leethomason/OpenSaber/parts/shapes.scad

FACES   = 180;
EPSILON = 0.1;
PIN	    = 2.54;


module tube(h=1, inner=0, outer=0, di=0, do=0) {
    rInner = inner > 0 ? inner : di / 2;
    rOuter = outer > 0 ? outer : do / 2;

	if (rInner >= rOuter) echo("ERROR in tube. rOuter must be > rInner.");

	difference() {
		cylinder(h=h, r=rOuter);
		translate([0,0,-EPSILON]) {
			cylinder(h=h + EPSILON*2, r=rInner);
		}
	}
}

module roundedRect(size, r, up="z")
{
	if (up == "x") {
		H = size[0];
		hull()
		{
			translate([0, r, r]) rotate([0, 90, 0]) cylinder(r=r, h=H);
			translate([0, size[1] - r, r]) rotate([0, 90, 0]) cylinder(r=r, h=H);
			translate([0, r, size[2] - r]) rotate([0, 90, 0]) cylinder(r=r, h=H);
			translate([0, size[1] - r, size[2] - r]) rotate([0, 90, 0]) cylinder(r=r, h=H);
		}
	}
	else if (up == "y") {
		H = size[1];
		hull()
		{
			translate([r, 0, r]) rotate([-90, 0, 0]) cylinder(r=r, h=H);
			translate([size[0] - r, 0, r]) rotate([-90, 0, 0]) cylinder(r=r, h=H);
			translate([r, 0, size[2] - r]) rotate([-90, 0, 0]) cylinder(r=r, h=H);
			translate([size[0] - r, 0, size[2] - r]) rotate([-90, 0, 0]) cylinder(r=r, h=H);
		}
	}
	else {
		H = size[2];
		hull()
		{
			translate([r, r, 0])  cylinder(r=r, h=H);
			translate([size[0] - r, r, 0])  cylinder(r=r, h=H);
			translate([r, size[1] - r, 0])  cylinder(r=r, h=H);
			translate([size[0] - r, size[1] - r, 0])  cylinder(r=r, h=H);
		}
	}
}

module cubePair(x, size)
{
	translate([x, 0, 0])
		cube(size=size);
	mirror([1,0,0]) translate([x, 0, 0])
		cube(size=size);
}

module polygonXY(h, points)
{
    linear_extrude(height = h) {
        polygon(points=points);
    }  
}

module polygonYZ(h, points)
{
    multmatrix(m = [ [0, 0, 1, 0],
    				 [1, 0, 0, 0],
    				 [0, 1, 0, 0],
    				 [0, 0, 0, 1]
       			   ])
    linear_extrude(height = h) {
        polygon(points=points);
    }  	
}

module polygonZY(h, points)
{
    multmatrix(m = [ [0, 0, 1, 0],
    				 [0, 1, 0, 0],
    				 [1, 0, 0, 0],
    				 [0, 0, 0, 1]
       			   ])
    linear_extrude(height = h) {
        polygon(points=points);
    }  	
}
module polygonXZ(h, points)
{
    multmatrix(m = [ [1, 0, 0, 0],
    				 [0, 0, 1, 0],
    				 [0, 1, 0, 0],
    				 [0, 0, 0, 1]
       			   ])
    linear_extrude(height = h) {
        polygon(points=points);
    }  	
}


module zCapsule(dz0, dz1, r, roundedRect=0)
{
	if (roundedRect == 0) {
		hull() {
			translate([0, 0, dz0]) rotate([-90, 0, 0]) cylinder(h=50, r=r);
			translate([0, 0, dz1]) rotate([-90, 0, 0]) cylinder(h=50, r=r);
		}
	}
	else {
		if (dz1 < dz0) {
			t = dz0;
			dz0 = dz1;
			dz1 = t;
		}
		hull() {
			translate([r - roundedRect, 0, dz0 - r + roundedRect]) 
				rotate([-90, 0, 0]) cylinder(h=50, r=roundedRect);
			translate([-r + roundedRect, 0, dz0 - r + roundedRect]) 
				rotate([-90, 0, 0]) cylinder(h=50, r=roundedRect);
			translate([r - roundedRect, 0, dz1 + r - roundedRect]) 
				rotate([-90, 0, 0]) cylinder(h=50, r=roundedRect);
			translate([-r + roundedRect, 0, dz1 + r - roundedRect]) 
				rotate([-90, 0, 0]) cylinder(h=50, r=roundedRect);
		}
	}
}

module xRoofCube(size)
{
	x = size[0];
	y = size[1];
	z = size[2];

	polygonXY(h=z, points=[
		[0, 0],
		[x, 0],
		[x, y + x],		// gets the 45 degree angle for printing
		[0, y]
	]);
}

module tubeTriTop(h, do, di, theta=50) {
	tube(h=h, di=di, do=do);
	intersection() {
		cylinder(h=h, d=do);
		a = di / 2;
		b = a / tan(theta);
		union() {
			polygonXY(h=h, points=[
				[0, a], [a, a], [a, a - b]
			]);
			mirror([-1, 0, 0]) polygonXY(h=h, points=[
				[0, a], [a, a], [a, a - b]
			]);
		}
	}
}
