leethomason/OpenSaber/parts/aquatic/alignment.scad

$fn = 180;
difference() {
    cylinder(h=2, d=16.6);
    cylinder(h=2, d=3,2);
}
