leethomason/OpenSaber/parts/clan/dim_aeonv4.scad

HAS_FORE_AFT = true;            // has 2 different bores
HAS_COUPLER = 2;                // 0: none, 1: header, 2: thread
HAS_PIN_IGNITION = false;       // if true, small pin, else proper switch
HAS_KEYJOINT_PILLAR = false;    // reinforces the key joint - small sabers
ALLOW_POWER_NUT_TO_TURN = false;
COVERTEC_CUTOUT = 0;
FORE_THERMAL_RELIEF = true;

D_OUTER = 37.25;
D_AFT_INNER = 32.5 + 0.2;
D_FORE_INNER = 25.4;
DZ_AFT = 113.2;
DZ_TOTAL = DZ_AFT + 100; // just defines inner()

DZ_SPEAKER = 12.0;
D_PLATE_PORT = 11.0;
NUM_VENTS = 10;              // if 0, no side vents

M_0 = 0.0;
M_MC = 10.0;
M_FORE = DZ_AFT;

RIDGE = 120.34;
M_SWITCH_CENTER = RIDGE + 55.9 + 16.0/2.0; // center of ORIGINAL switch

DZ_PLATE = 36.0;
W_PLATE = 17.0;
M_PLATE = M_SWITCH_CENTER - DZ_PLATE / 2;
DY_FLAT = 1.5;

PLATE_PAD = 2.0;
M_BOLT = M_SWITCH_CENTER + 1.0;
M_PORT = M_SWITCH_CENTER - DZ_PLATE / 2 + PLATE_PAD + D_PLATE_PORT / 2;
M_SWITCH = M_SWITCH_CENTER + DZ_PLATE / 2 - PLATE_PAD - 8.2 / 2;
M_COUPLER_START = M_SWITCH + 8.0;

KEYJOINT = 8;
KEYJOINT_T = 5.0;
