leethomason/OpenSaber/parts/clan/dim_initiate.scad

HAS_FORE_AFT = true;            // has 2 different bores
HAS_COUPLER = 3;                // 0: none, 1: header, 2: thread, 3: short-thread
HAS_PIN_IGNITION = false;        // if true, small pin, else proper switch
HAS_KEYJOINT_PILLAR = false;    // reinforces the key joint - small sabers
HAS_SIDE_VENTS = true;          // side vents on front part
ALLOW_POWER_NUT_TO_TURN = false;
COVERTEC_CUTOUT = 0;

D_OUTER = 37.33;
D_AFT_INNER = 32.5;
D_FORE_INNER = 25.4;
DZ_AFT = 114.29;
DZ_TOTAL = 114.29 + 100; // just defines inner()

DZ_SPEAKER = 14.5;
D_PLATE_PORT = 11.0;

M_0 = 0.0;
M_MC = -12.0;
M_FORE = DZ_AFT;
M_SWITCH_CENTER = 137.31 + 16.0/2.0; // center of ORIGINAL switch

DZ_PLATE = 32.0;
W_PLATE = 17.0;
M_PLATE = M_SWITCH_CENTER - DZ_PLATE / 2;
DY_FLAT = 1.5;
NUM_VENTS = 6;

PLATE_PAD = 1.0;
M_BOLT = M_SWITCH_CENTER + 1.0;
M_PORT = M_SWITCH_CENTER - DZ_PLATE / 2 + PLATE_PAD + D_PLATE_PORT / 2;
M_SWITCH = M_SWITCH_CENTER + DZ_PLATE / 2 - PLATE_PAD - 8.2 / 2;
M_COUPLER_START = M_SWITCH + 6.0;

KEYJOINT = 8;
KEYJOINT_T = 5.0;
