leethomason/OpenSaber/parts/darksaber/killkey.scad

$fn = 40;

difference() {
    cylinder(h=7.0, d=13.5);
    translate([2, 0, -0.001]) cylinder(h=4.0, d=5.6);
}
