leethomason/OpenSaber/parts/duchess/dim.scad

use <../commonUnified.scad>
M_0 = 0;

// Test trims - rather tight.
M_START = -(41.5 - 0.40*25.4);
M_MC = -19.0;
DZ_SPKR = M_MC - M_START;
M_MC_BATTERY = M_START + DZ_SPKR;

DZ_BODY = 101.6;
M_AFT_FRONT = DZ_BODY - 10.5 - 0.5;
M_TRANSITION_RING = DZ_BODY - 15.0;
M_COUPLER_START = M_AFT_FRONT + 1.0;

DZ_AFT = M_AFT_FRONT - M_START;

D_VENT = 26.0;
D_VENT_BOLT = 13.5;     // guess...
D_VENT_INNER = 20.60;    // coupler is 20.24

D_INNER = 31.60;    // 31.7 is fine for the body, but too tight for the pommel
D_OUTER = 36.9;

DZ_BAFFLE = 3.0;

N_BATT_BAFFLES = nBafflesNeeded(DZ_BAFFLE, "18650");
M_JOINT = M_MC_BATTERY + zLenOfBaffles(N_BATT_BAFFLES, DZ_BAFFLE);

DZ_POWER_RING = 18.0;
DZ_BOLT = 8.0;          // switch to allen head for space?
DZ_SWITCH = (M_AFT_FRONT - M_JOINT - DZ_POWER_RING - DZ_BOLT);

DZ_RING0 = 3.0; // thickness of the aft vent coupler
DZ_RING1 = 2.5; // fore vent coupler (non-standard)
DZ_FORE_SUPPORT = 1.5;

DZ_FORE_FULL = M_AFT_FRONT - M_JOINT;
DZ_FORE_TRIM = DZ_FORE_FULL - DZ_RING0;

M_BOLT_START = M_JOINT + DZ_POWER_RING;
M_SWITCH_START = M_BOLT_START + DZ_BOLT;

M_BOLT = M_BOLT_START + DZ_BOLT / 2;
M_PORT = M_JOINT + DZ_POWER_RING / 2;
M_SWITCH = M_SWITCH_START + DZ_SWITCH / 2;

INSET_W = 14.0;
D_RING = 33.4;

DX_SWITCH_PLATE = 16.5;

D_TUBE = 4.6;
D_TUBE_INNER = 3.3;
D_ROD = 3.6;
D_BOLT_CAP = 7.0;
D_HOLDER = 8.0;
