leethomason/OpenSaber/parts/duchess2/dim.scad

use <../commonUnified.scad>
M_0 = 0;

// Test trims - rather tight.
M_START = -(41.5 - 0.40*25.4);
M_MC = -19.0;
DZ_SPKR = M_MC - M_START;

DZ_BODY = 101.6; // MHS part
M_AFT_FRONT = DZ_BODY - 10.5 - 0.5; // front of the microcontroller section.
DZ_AFT = M_AFT_FRONT - M_START;

D_VENT_OUTER = 36.8;
D_VENT_INNER = 25.8;

D_INNER = 31.60;    // 31.7 is fine for the body, but too tight for the pommel
D_OUTER = 36.9;

DZ_BAFFLE = 3.0;

N_BATT_BAFFLES = nBafflesNeeded(DZ_BAFFLE, "18650");
M_JOINT = M_MC + zLenOfBaffles(N_BATT_BAFFLES, DZ_BAFFLE);

DZ_POWER_RING = 18.0;
DZ_BOLT = 8.0;          // switch to allen head for space?
DZ_SWITCH = (M_AFT_FRONT - M_JOINT - DZ_POWER_RING - DZ_BOLT);

M_BOLT_START = M_JOINT + DZ_POWER_RING;
M_SWITCH_START = M_BOLT_START + DZ_BOLT;

M_BOLT = M_BOLT_START + DZ_BOLT / 2;
M_PORT = M_JOINT + DZ_POWER_RING / 2;
M_SWITCH = M_SWITCH_START + DZ_SWITCH / 2;

M_RING0_CENTER = DZ_BODY + 6.0;
M_RING1_CENTER = DZ_BODY + 22.2;
M_RING2_CENTER = DZ_BODY + 38.0;

M_EMITTER = 175.8;
M_EMITTER_PLATE = M_EMITTER - 15.7;
M_FOOTER = M_EMITTER_PLATE - 11.0;
M_FOOTER_RING = M_FOOTER - 4.0;

INSET_W = 14.0;
D_RING = 33.4;

DX_SWITCH_PLATE = 16.5;

D_ROD = 3.4;
D_ROD_LOOSE = 3.6;  // FIXME
D_ROD_NUT = 7.3;    // space for a nut to thread. New small ones!
D_TUBE = 4.4;       // outer radius of tube that carries power to emitter
D_TUBE_INNER = 3.2; // FIXME
D_CRYSTAL_SPACE = 12.0;

HEAD_HOLDER_SETBACK = 4.0;  // how deep threads go into pillars
TUBE_HOLDER_SETBACK = 2.0;  // how deep the tubes are seated

A_TILT = -65;
A_BOLT_0 = 90 + A_TILT;     // angle of bolt
A_BOLT_1 = 270 + A_TILT;    // angle of bolt
ANGLE_OFFSET = 33;          // from rod to tube

A_CHAMBER_CUT_0 = -15 + A_TILT;
A_CHAMBER_CUT_1 = 15 + A_TILT;
A_CHAMBER_CUT_2 = 45 + A_TILT;
R_CHAMBER_CUT = 9.5;
D_CHAMBER_CUT = 3.6;

CHAMBER_RING_DZ = 1.5 * 2 + 3.0; // guess - thickness of brass, working space inside
T_BRASS = 1.4;
DZ_CHAMBER_BASE = 6;
