leethomason/OpenSaber/parts/knight/plug.scad

$fn=90;
cylinder(h=4, d=25.4);
cylinder(h=7, d=18.6);
