leethomason/OpenSaber/parts/leia/dim.scad

M_0 = 0;
M_FORE = 91.4;
M_T = M_FORE;
DZ_FORE = 104.0;
DZ_FORE_OUTER = 4.0 * 25.4;
M_FORE_END = M_T + DZ_FORE;

D_INNER_AFT = 31.5;
D_OUTER_AFT = 41.7;
D_INNER_FORE = 29.0;

DZ_BUTTRESS = 4.0;
DZ_THREAD = 10.0;

DZ_INSET = 42.4;    // could be 40
DX_INSET = 18.0;
Z_END_INSET   = M_T - DZ_THREAD - 1.8;

BOLT_TO_PORT = 12.0;  // has to be forward to clear the microcontroller
BOLT_TO_SWITCH = -12.0;

D_BUTTON_HEAD = 9.0;    // fixme
