leethomason/OpenSaber/parts/leia/killkeyholder.scad

use <../shapes.scad>
$fn = 80;
TRIM = 0.3;
tube(h=6.0, do=11.0-TRIM, di=5.45+TRIM);
