leethomason/OpenSaber/parts/leia_ps/killkey.scad

$fn = 40;

difference() {
    cylinder(h=8.0, d=8.5);
    cylinder(h=5.0, d=5.6);
}
