leethomason/OpenSaber/src/i2saudio2/i2saudio2.ino

#include "src/wav12/expander.h"
#include "src/wav12/s4adpcm.h"
#include "src/wav12util/manifest.h"
#include "src/i2saudio2/i2saudiodrv.h"
#include "src/util/Grinliz_Util.h"
#include "src/nada_flashmem/Nada_FlashTransport_SPI.h"
#include "src/nada_flashmem/Nada_SPIFlash.h"

#include <Adafruit_ZeroI2S.h>
#include <Adafruit_ZeroDMA.h>

//#define LOG_PERF

Nada_FlashTransport_SPI flashTransport(SS1, &SPI1);
Nada_SPIFlash spiFlash(&flashTransport);

Adafruit_ZeroDMA dma;
Adafruit_ZeroI2S i2s(0, 1, 12, 2);
Manifest manifest;
I2SAudioDriver i2sAudioDriver(&dma, &i2s, &spiFlash, manifest);
MemPalette memPalette[MemPalette::NUM_PALETTES];
CStr<64> descString;

static const int TEST_SOURCE_SAMPLES = 1024;
static const int TEST_COMPRESSED_BYTES = 512;

int16_t gSourceSamples[TEST_SOURCE_SAMPLES];
uint8_t gCompressed[TEST_COMPRESSED_BYTES];
int32_t gTarget[TEST_SOURCE_SAMPLES*2];

int currentDir = 0;
int nRunsPerSec = 0;

void scan()
{
    Log.p("p: play track channel=0").eol();
    Log.p("l: loop track channel=0").eol();
    Log.p("s: stop channel (stop all if no channel)").eol();
    Log.p("v: volume value=0,256+ channel").eol();
    Log.p("d: directory display").eol();

    int start = 0, count = 0;
    manifest.dirRange(currentDir, &start, &count);
    Log.p("Dir range. start=").p(start).p(" count=").p(count).eol();
    for(int i=0; i<count; ++i)
        dumpMemUnit(i + start, manifest.getUnit(i + start));

}

void dumpMemUnit(int id, const MemUnit& memUnit)
{
    char name[9] = {0};
    memcpy(name, memUnit.name, 8);

    Log.p("[").p(id).p("] ").p(name).p(" addr=").p(memUnit.offset).p(" size=").p(memUnit.size)
       .p(" table=").p(memUnit.table)
       .p(" samples=").p(memUnit.numSamples())
      .eol();
}

void dumpConfig()
{
    Log.p("Desc=").p(descString.c_str()).eol();
    for(int i=0; i<MemPalette::NUM_PALETTES; ++i) {
        Log.p("Palette: ")
            .p(i).p(" font=").p(memPalette[i].soundFont)
            .p(" bc=").v3(memPalette[i].bladeColor.r, memPalette[i].bladeColor.g, memPalette[i].bladeColor.b)
            .p(" ic=").v3(memPalette[i].impactColor.r, memPalette[i].impactColor.g, memPalette[i].impactColor.b)
            .eol();
    }
}

void processCmd(const CStr<32>& str) 
{
    CStr<32> action, str0, str1;
    CStr<32>* arr[3] = { &action, &str0, &str1};
    str.tokenize(' ', arr, 3);
    int value0 = -1, value1 = -1;
    if (!str0.empty()) value0 = atoi(str0.c_str());
    if (!str1.empty()) value1 = atoi(str1.c_str());

    //Log.p("process: ").p(action.c_str()).p(" ").pt(str0).p(" ").pt(str1).eol();

    if (action == 'p') {
        if (value1 < 0) value1 = 0;
        Log.p("Play track=").p(value0).p(" channel=").p(value1).eol();
        i2sAudioDriver.play(value0, false, value1);
    }
    else if (action == 'l') {
        if (value1 < 0) value1 = 0;
        Log.p("Loop track=").p(value0).p(" channel=").p(value1).eol();
        i2sAudioDriver.play(value0, true, value1);
    }
    else if (action == 's') {
        if (value0 >= 0) {
            Log.p("Stop channel=").p(value0).eol();
            i2sAudioDriver.stop(value0);
        }
        else {
            Log.p("Stop all.").eol();
            for(int i=0; i<AUDDRV_NUM_CHANNELS; ++i) {
                i2sAudioDriver.stop(i);
            }
        }
    }
    else if (action == 'v') {
        if (value1 < 0) value1 = 0;

        if (value0 >= 0 && value1 >= 0) {
            Log.p("Volume=").p(value0).p(" channel=").p(value1).eol();
            i2sAudioDriver.setVolume(value0, value1);
        }
        else if (value0 >= 0) {
            Log.p("Volume=").p(i2sAudioDriver.getVolume(value0)).eol();
        }
    }
    else if (action == 'd') {
        for(int i=0; i<AUDDRV_NUM_CHANNELS; ++i) {
            i2sAudioDriver.stop(i);
        }
        if (value0 >=0 && value0 < 4) {
            currentDir = value0;
            scan();
        }
    }
}

void setup()
{
    Serial.begin(19200);
    while (!Serial)
        delay(400);
    Log.attachSerial(&Serial);

    Log.p("Serial open.").eol();

    spiFlash.begin();
    spiFlash.readMemory(0, (uint8_t*) manifest.getBasePtr(), MemImage::SIZE_MEMUNITS);
    spiFlash.readMemory(Manifest::PaletteAddr(0), (uint8_t*) memPalette, MemImage::SIZE_PALETTE);
    spiFlash.readMemory(Manifest::DescAddr(), (uint8_t*) descString.c_str(), MemImage::SIZE_DESC);

    dumpConfig();

    i2sAudioDriver.begin();

    scan();
    Log.p("setup() complete.").eol();
}

CStr<32> cmd;

void loop()
{
    #ifdef LOG_PERF
    static uint32_t lastLoopTime = 0;
    static int nTestCall = 0;
    static int testHash = 0;

    uint32_t deltaMilli = millis() - lastLoopTime;
    testHash += test();
    ++nTestCall;
    static const int NSEC = 5;
    if (deltaMilli > NSEC * 1000) {

        Log.p("Time(indirect)%=").p(100 - (100 * nTestCall / (nRunsPerSec * NSEC)))
           .eol();
        nTestCall = 0;
        lastLoopTime = millis();
    }
    #endif

    while (Serial.available()) {
        int c = Serial.read();
        if (c == '\n') {
            //Log.pt(cmd).eol();
            processCmd(cmd);
            cmd.clear();
        }
        else {
            cmd.append(c);
        }
    }

}
