leethomason/OpenSaber/src/i2saudio2/src/i2saudio2/i2saudiodrv.cpp

/*
  Copyright (c) Lee Thomason, Grinning Lizard Software

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
  THE SOFTWARE IS PROVIDED "AS IS", WITHOUT WARRANTY OF ANY KIND, EXPRESS OR
  IMPLIED, INCLUDING BUT NOT LIMITED TO THE WARRANTIES OF MERCHANTABILITY,
  FITNESS FOR A PARTICULAR PURPOSE AND NONINFRINGEMENT. IN NO EVENT SHALL THE
  AUTHORS OR COPYRIGHT HOLDERS BE LIABLE FOR ANY CLAIM, DAMAGES OR OTHER
  LIABILITY, WHETHER IN AN ACTION OF CONTRACT, TORT OR OTHERWISE, ARISING FROM,
  OUT OF OR IN CONNECTION WITH THE SOFTWARE OR THE USE OR OTHER DEALINGS IN THE
  SOFTWARE.
*/

#include "i2saudiodrv.h"
#include "../util/Grinliz_Util.h"
#include "../wav12util/manifest.h"

#include <Arduino.h>
#include <Adafruit_ZeroI2S.h>
#include <Adafruit_ZeroDMA.h>

#include <stdint.h>

#define DECODE_NONE 0
#define DECODE_SIN  1
#define DECODE_S4   2
#define DECODE DECODE_S4

#define FILL_LEFT
#define FILL_RIGHT

//#define USE_16_BIT  // doesn't work - not sure if hardware or sw config
#define DEBUG_DEEP 1

#ifdef USE_16_BIT
int16_t stereoBuffer0[AUDDRV_STEREO_SAMPLES];
int16_t stereoBuffer1[AUDDRV_STEREO_SAMPLES];
#else
int32_t stereoBuffer0[AUDDRV_STEREO_SAMPLES] = {0};
int32_t stereoBuffer1[AUDDRV_STEREO_SAMPLES] = {0};
#endif
DmacDescriptor* descriptor = 0;

I2SAudioDriver::Status I2SAudioDriver::status[AUDDRV_NUM_CHANNELS];
bool I2SAudioDriver::isQueued[AUDDRV_NUM_CHANNELS];
SPIStream I2SAudioDriver::spiStream[AUDDRV_NUM_CHANNELS];
wav12::ExpanderAD4 I2SAudioDriver::expander[AUDDRV_NUM_CHANNELS];
int I2SAudioDriver::volume[AUDDRV_NUM_CHANNELS];

static volatile uint32_t callbackCycle = 0;

uint32_t I2SAudioDriver::stableSlowTime()
{
    uint32_t t0 = 0;
    uint32_t t1 = 1;
    while(t0 != t1) {
        t0 = callbackCycle;
        t1 = callbackCycle;
    }
    //static const uint32_t M = 1000 * AUDDRV_BUFFER_SAMPLES / AUDDRV_FREQ;    // 11.61 in theory.
    static const uint64_t M = 1161;

    uint64_t m = uint64_t(t0) * M / 100;
    return uint32_t(m);
}

void I2SAudioDriver::DMACallback(Adafruit_ZeroDMA* dma)
{
    callbackCycle++;
    #ifdef USE_16_BIT
    int16_t* src = (callbackCycle & 1) ? stereoBuffer1 : stereoBuffer0;
    int16_t* fill = (callbackCycle & 1) ? stereoBuffer0 : stereoBuffer1;
    #else
    int32_t* src  = (callbackCycle & 1) ? stereoBuffer1 : stereoBuffer0;
    int32_t* fill = (callbackCycle & 1) ? stereoBuffer0 : stereoBuffer1;
    #endif
    
    dma->changeDescriptor(descriptor, 
        src,                           // from here         
        (void *)(&I2S->DATA[0].reg),   // to here (M0+)
        AUDDRV_STEREO_SAMPLES);        // this many...

    dma->startJob();

    /* --- decode to fill --- */
#if DECODE == DECODE_S4

    for(int i=0; i<AUDDRV_NUM_CHANNELS; ++i) {
        if (isQueued[i]) {
            isQueued[i] = false;
            spiStream[i].set(status[i].addr, status[i].size);
            const int32_t* table = S4ADPCM::getTable(status[i].table);
            expander[i].init(&spiStream[i], table, status[i].predictor);
            expander[i].rewind();
        }
    }

    for(int i=0; i<AUDDRV_NUM_CHANNELS; ++i) {
        int n = 0;
        if (status[i].addr) {
            n = expander[i].expand(fill, AUDDRV_BUFFER_SAMPLES, volume[i], i > 0, false);

            if (status[i].loop && n < AUDDRV_BUFFER_SAMPLES) {
                expander[i].rewind();
                expander[i].expand(fill + n*2, AUDDRV_BUFFER_SAMPLES - n, volume[i], i > 0, false);
                n = AUDDRV_BUFFER_SAMPLES;
            }
        }
        if (i == 0 && n < AUDDRV_BUFFER_SAMPLES) {
            for(int j=n; j<AUDDRV_BUFFER_SAMPLES; ++j) {
                fill[j*2 + 0] = 0;
                fill[j*2 + 1] = 0;
            }
        }
    }
#endif
#if DECODE == DECODE_SIN
    static uint32_t t = 0;
    static const int TEST_FREQ = 220;
    static const uint32_t MULT = 32768 * TEST_FREQ / AUDDRV_FREQ;

    for(int i=0; i<AUDDRV_BUFFER_SAMPLES; i++, t++) {
        #ifdef USE_16_BIT
        int16_t val = iSin_S3(t * MULT);
        #else
        int32_t val = iSin_S3(t * MULT) * 16000 * 4;
        #endif
        #ifdef FILL_LEFT
        fill[i*2 + 0] = val;
        #endif
        #ifdef FILL_RIGHT
        fill[i*2 + 1] = val;
        #endif
        ++t;
    }
#endif    
}

void I2SAudioDriver::begin()
{
    Log.p("I2SAudioDriver::begin starting.").eol();

    for(int i=0; i<AUDDRV_NUM_CHANNELS; ++i) {
        spiStream[i].init(spiFlash);
        expander[i].init(&spiStream[i], S4ADPCM::getTable(0), S4ADPCM::State::PREDICTOR);   
        volume[i] = 64;
    }

    Log.p("DMA Configure.").eol();
    dma->setTrigger(I2S_DMAC_ID_TX_0);
    dma->setAction(DMA_TRIGGER_ACTON_BEAT);

    Log.p("Allocating DMA channel:").eol();
    ZeroDMAstatus stat = dma->allocate();
    dma->printStatus(stat);

    Log.p("Setting up transfer").eol();
    descriptor = dma->addDescriptor(
        stereoBuffer0,                // move data from here
        (void *)(&I2S->DATA[0].reg),  // to here (M0+)
        AUDDRV_STEREO_SAMPLES,        // this many...
        #ifdef USE_16_BIT
        DMA_BEAT_SIZE_HWORD,          // bytes/hword/words
        #else
        DMA_BEAT_SIZE_WORD,           // bytes/hword/words
        #endif
        true,                         // increment source addr?
        false);

    dma->loop(false);
    Log.p("Adding callback").eol();
    dma->setCallback(DMACallback);
    Log.p("DMA configuration done. Starting I2S").eol();

#ifdef USE_16_BIT
    i2s->begin(I2S_16_BIT, AUDDRV_FREQ);
#else
    i2s->begin(I2S_32_BIT, AUDDRV_FREQ);
#endif
    i2s->enableTx();

    Log.p("I2S started. Starting DMA job.").eol();
    stat = dma->startJob();
    Log.p("I2SAudioDriver begin() complete.").eol();
}


void I2SAudioDriver::play(int index, bool loop, int channel)
{
    // Log.p("I2SAudioDriver::play index=").p(index).p(" loop=").p(loop).p(" ch=").p(channel).eol();
    channel = glClamp(channel, 0, AUDDRV_NUM_CHANNELS - 1);
    const MemUnit& memUnit = manifest.getUnit(index);

    noInterrupts();
    status[channel].addr = memUnit.offset;
    status[channel].size = memUnit.size;
    status[channel].table = memUnit.table;
    status[channel].predictor = memUnit.predictor;
    status[channel].loop = loop;
    isQueued[channel] = true;
    interrupts();
}


bool I2SAudioDriver::isPlaying(int channel)
{
    channel = glClamp(channel, 0, AUDDRV_NUM_CHANNELS-1);
    noInterrupts();
    bool playing = !expander[channel].done();
    playing |= isQueued[channel];
    interrupts();
    return playing;    
}


void I2SAudioDriver::stop(int channel)
{
    channel = glClamp(channel, 0, AUDDRV_NUM_CHANNELS - 1);

    noInterrupts();
    status[channel].clear();
    isQueued[channel] = true;
    interrupts();
}


void I2SAudioDriver::setVolume(int v, int channel)
{
    channel = glClamp(channel, 0, AUDDRV_NUM_CHANNELS - 1);
    v = glClamp(v, 0, 512);   // the 512 is arbitrary, but some sort of limit is good
    volume[channel] = v;
}


int I2SAudioDriver::getVolume(int channel)
{
    channel = glClamp(channel, 0, AUDDRV_NUM_CHANNELS - 1);
    return volume[channel];
}
