leethomason/OpenSaber/src/lsm303/swing.h

/*
  Copyright (c) Lee Thomason, Grinning Lizard Software

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
  THE SOFTWARE IS PROVIDED "AS IS", WITHOUT WARRANTY OF ANY KIND, EXPRESS OR
  IMPLIED, INCLUDING BUT NOT LIMITED TO THE WARRANTIES OF MERCHANTABILITY,
  FITNESS FOR A PARTICULAR PURPOSE AND NONINFRINGEMENT. IN NO EVENT SHALL THE
  AUTHORS OR COPYRIGHT HOLDERS BE LIABLE FOR ANY CLAIM, DAMAGES OR OTHER
  LIABILITY, WHETHER IN AN ACTION OF CONTRACT, TORT OR OTHERWISE, ARISING FROM,
  OUT OF OR IN CONNECTION WITH THE SOFTWARE OR THE USE OR OTHER DEALINGS IN THE
  SOFTWARE.
*/

#pragma once

#include <stdint.h>
#include "./src/util/Grinliz_Util.h"

#ifdef _MSC_VER
#define FILTER_MAG_X	4
#define FILTER_MAG_Y	4
#define FILTER_MAG_Z	4
#define SWING_SAMPLES	8
#else
#include "pins.h"	// for SWING_SAMPLES and FILTER_MAG_X/Y/Z
#endif

/*
// The FILTER constants run an average over the accelerometer
// data. They are turned first, to get stable accelerometer
// readings when the saber is on or off.
#	define FILTER_MAG_X	10
#	define FILTER_MAG_Y	10
#	define FILTER_MAG_Z	10
// SWING_SAMPLES further filters the actual swing. It is 
// frustrating that the FILTER_ isn't enough. If this is
// too large, the swing sound will trail the motion. If too
// small, dead spots become annoying.
#	define SWING_SAMPLES 8
// The maximum rad/sec of the swing. Used for the sound envelope.
#	define SWING_MAX 16
*/
/*
The Swing algorithm translation rotation of the blade into sound level.
It is currently based on an LSM303 accel + mag chip. Some notes:

- An accel + gyro would be better; the output of a gyro is, after all,
  the number we are trying to get. But that takes another chip on the board
  and has it's own challenges, in terms of board layout and yield.
- The mag is *very* noisy, tuned above.
- The swing is still noisier than expected.
- There are dead spots in the mag reading - from local fields or sensor orientation?
*/

class Swing
{
public:
	Swing();

	void push(const Vec3<int32_t>& x, const Vec3<int32_t>& xMin, const Vec3<int32_t>& xMax);
	// speed in radians / second
	float speed() const { return m_speed; }
	// from -1 to 1
	float dotOrigin() const { return m_dot;}

	void setOrigin() { m_setOrigin = true;}

	static bool test();

private:
	Vec3<float> calcVec(const Vec3<int32_t>& vec, const Vec3<int32_t>& mMin, const Vec3<int32_t>& mMax) const;
  float calcDot(const Vec3<int32_t>& x, const Vec3<int32_t>& mMin, const Vec3<int32_t>& mMax) const;

	bool m_init = false;
	bool m_setOrigin = false;
	float m_speed = 0;	
	float m_dot = 0;
	Vec3<float> m_dotOrigin;
	AverageSample<int32_t, SWING_SAMPLES> swingAve;
	AverageSample<int32_t, FILTER_MAG_X> xInputAve;
	AverageSample<int32_t, FILTER_MAG_Y> yInputAve;
	AverageSample<int32_t, FILTER_MAG_Z> zInputAve;
};
