leethomason/OpenSaber/src/saber/bladecolor.cpp

/*
  Copyright (c) Lee Thomason, Grinning Lizard Software

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
  THE SOFTWARE IS PROVIDED "AS IS", WITHOUT WARRANTY OF ANY KIND, EXPRESS OR
  IMPLIED, INCLUDING BUT NOT LIMITED TO THE WARRANTIES OF MERCHANTABILITY,
  FITNESS FOR A PARTICULAR PURPOSE AND NONINFRINGEMENT. IN NO EVENT SHALL THE
  AUTHORS OR COPYRIGHT HOLDERS BE LIABLE FOR ANY CLAIM, DAMAGES OR OTHER
  LIABILITY, WHETHER IN AN ACTION OF CONTRACT, TORT OR OTHERWISE, ARISING FROM,
  OUT OF OR IN CONNECTION WITH THE SOFTWARE OR THE USE OR OTHER DEALINGS IN THE
  SOFTWARE.
*/

#include "bladecolor.h"
#include "./src/util/Grinliz_Util.h"
#include "rgb2hsv.h"
#include "./src/util/fixed.h"
#include "rgb.h"

void BladeColor::tick(uint32_t msec)
{
    if (msec - tStart >= LEN) {
        color = bladeColor;
    }
    else {
        uint32_t t = uint32_t(msec - tStart) * 1024 / LEN;

        color.r = lerp1024(impactColor.r, bladeColor.r, t);
        color.g = lerp1024(impactColor.g, bladeColor.g, t);
        color.b = lerp1024(impactColor.b, bladeColor.b, t);
    }
}


osbr::RGB ColorRotated(const osbr::RGB& rgb, int angle360)
{
    uint8_t h, s, v;
    rgb2hsv(rgb.r, rgb.g, rgb.b, &h, &s, &v);
    h += angle360 / 2;
    osbr::RGB c;
    hsv2rgb(h, s, v, &c.r, &c.g, &c.b);
    return c;
}



osbr::RGB AccelToColor(FixedNorm x, FixedNorm z)
{
    // x and z are in acceleration (g)
    // atan2 from -pi to pi
    FixedNorm angle = atan2(x, z) / kPi_FixedNorm;

    if (angle < FixedNorm{ 0 })
        angle = -angle;

    // range is now 0 to pi
    osbr::RGB rgb;
    hsv2rgb(scale(angle, 180), 255, 255, &rgb.r, &rgb.g, &rgb.b);
    return rgb;
}


bool TestAccelToColor()
{
    osbr::RGB rgb;

    // start out with basics.
    hsv2rgb(0, 255, 255, &rgb.r, &rgb.g, &rgb.b);
    TEST_IS_TRUE(rgb == osbr::RGB(255, 0, 0));

    hsv2rgb(90/2, 255, 255, &rgb.r, &rgb.g, &rgb.b);
    TEST_IS_TRUE(rgb == osbr::RGB(128, 255, 0));

    hsv2rgb(180 / 2, 255, 255, &rgb.r, &rgb.g, &rgb.b);
    TEST_IS_TRUE(rgb == osbr::RGB(0, 255, 255));

    hsv2rgb(270 / 2, 255, 255, &rgb.r, &rgb.g, &rgb.b);
    TEST_IS_TRUE(rgb == osbr::RGB(128, 0, 255));

    // z as blade: straight down (-1) to straight up (1)
    rgb = AccelToColor(FixedNorm{ 0 }, FixedNorm{ 1 });  // 0 -> 0
    TEST_IS_TRUE(rgb == osbr::RGB(255, 0, 0));

    rgb = AccelToColor(FixedNorm{ 0 }, FixedNorm{ -1 });  // 180 -> 360
    TEST_IS_TRUE(rgb == osbr::RGB(255, 0, 0));

    rgb = AccelToColor(FixedNorm{ 1 }, FixedNorm{ 0 });   // 90 -> 180
    TEST_IS_TRUE(rgb == osbr::RGB(0, 255, 255));

    rgb = AccelToColor(kSqrt2Over2_FixedNorm, kSqrt2Over2_FixedNorm); // 45 -> 90
    TEST_IS_TRUE(rgb == osbr::RGB(128, 255, 0));                

    rgb = AccelToColor(kSqrt2Over2_FixedNorm, -kSqrt2Over2_FixedNorm); // 135 -> -90
    TEST_IS_TRUE(rgb == osbr::RGB(128, 0, 255));

    return true;
}
