leethomason/OpenSaber/src/lsm303/pins.h

#pragma once

#if 1
#define FILTER_MAG_X	4
#define FILTER_MAG_Y	4
#define FILTER_MAG_Z	4
#define SWING_SAMPLES	8
#endif
#if 0
#define FILTER_MAG_X	8
#define FILTER_MAG_Y	8
#define FILTER_MAG_Z	8
#define SWING_SAMPLES	8
#endif
